cycfi/nu/cad_drawings/nu_multi/nu_multi_7_drawing.pdf

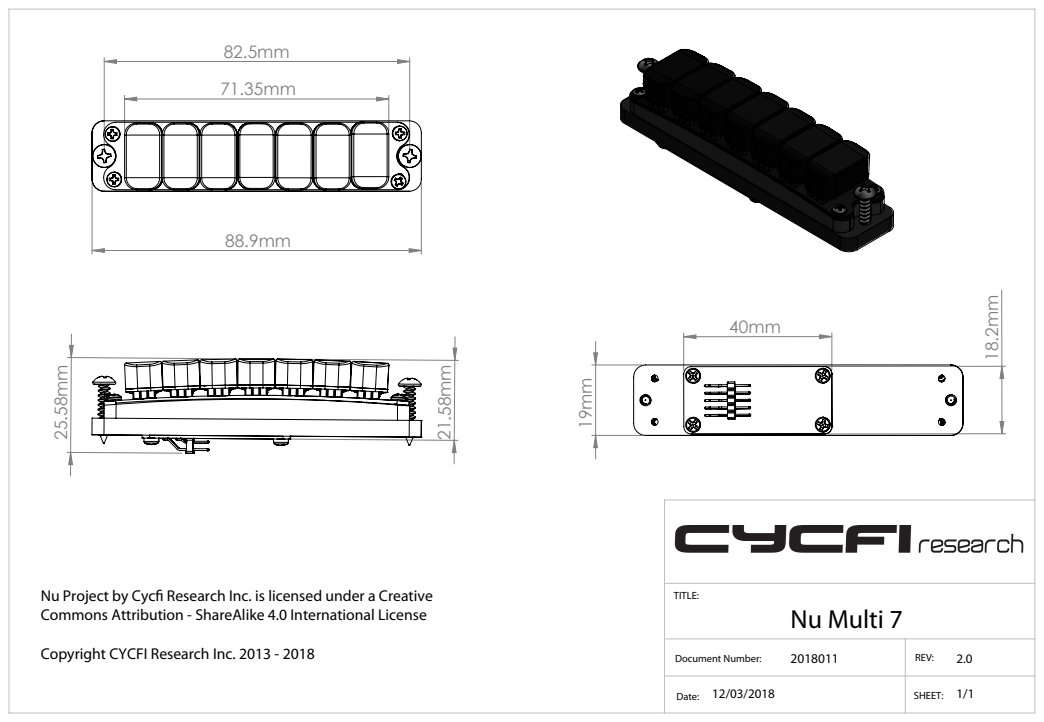
[picture p17: page 1]
Nu Multi 7; TITLE:

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

Copyright CYCFI Research Inc. 2013 - 2018

Document Number: 2018011 | REV: 2.0

12/03/2018 Date: | 1/1 SHEET:
