cycfi/nu/cad_drawings/nu_multi/nu_multi_8_drawing.pdf

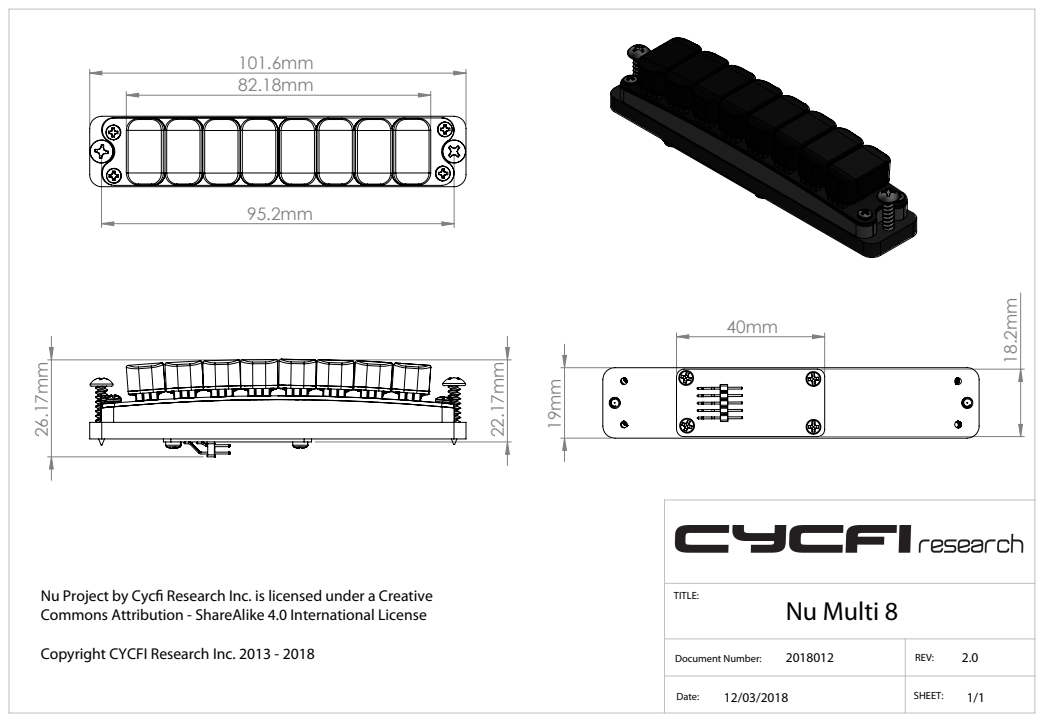
[picture p18: page 1]
Nu Multi 8; TITLE:

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

Copyright CYCFI Research Inc. 2013 - 2018

Document Number: 2018012 | REV: 2.0

Date: 12/03/2018 | SHEET: 1/1
